can-caglar/Data-Logger-STM32/resource/HoC.png

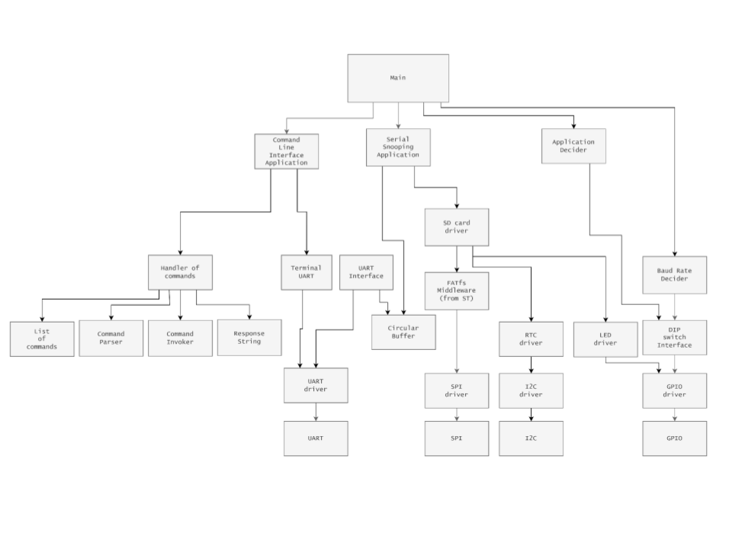
resource/HoC.png
