can-caglar/Data-Logger-STM32/resource/prototype.png

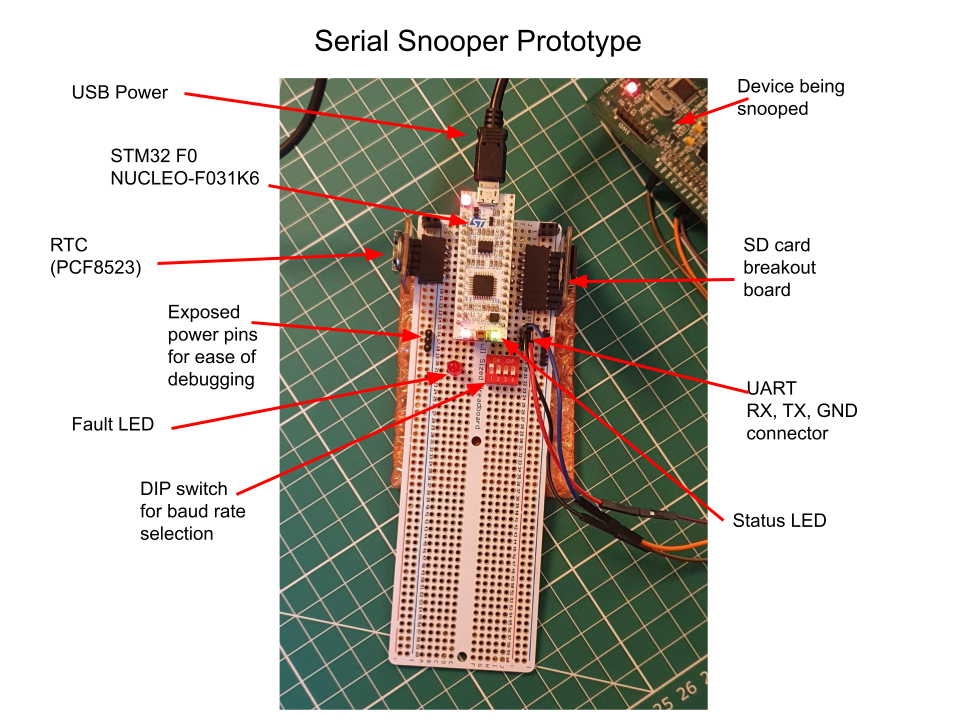
resource/prototype.png
