can-caglar/Data-Logger-STM32/src/serial_snooper/SerialSnooper.h

#ifndef SERIAL_SNOOPER_H
#define SERIAL_SNOOPER_H

#include <stdint.h>

#ifndef bool
#define bool uint8_t
#define true 1
#define false 0
#endif

enum
{
    SS_ERR_NONE,
    SS_ERR_FAULT,
};

#define MAX_TASKS 5

// Fw declare DataContext
typedef struct DataContext DataContext;

// Scheduler task function pointer
typedef void (*FnTask)(void);

void SerialSnooper_Init(void);
void SerialSnooper_Run(void);

int SerialSnooper_AddTask(FnTask func, 
    uint32_t period, bool periodic, bool enabled);

#endif
