can-caglar/Data-Logger-STM32/src/RTC/MyTimeString.c

#include "MyTimeString.h"
#include "MyRTC.h"
#include <stdio.h>
#include <string.h>

static const char* strLookup(uint8_t num);

static char ret[23];

#define LOOKUP_AMOUNT 100

static const char* const numToStrLookup[LOOKUP_AMOUNT] =
{
    "00", "01", "02", "03", "04",
    "05", "06", "07", "08", "09",
    "10", "11", "12", "13", "14",
    "15", "16", "17", "18", "19",
    "20", "21", "22", "23", "24",
    "25", "26", "27", "28", "29",
    "30", "31", "32", "33", "34",
    "35", "36", "37", "38", "39",
    "40", "41", "42", "43", "44",
    "45", "46", "47", "48", "49",
    "50", "51", "52", "53", "54",
    "55", "56", "57", "58", "59",
    "60", "61", "62", "63", "64",
    "65", "66", "67", "68", "69",
    "70", "71", "72", "73", "74",
    "75", "76", "77", "78", "79",
    "80", "81", "82", "83", "84",
    "85", "86", "87", "88", "89",
    "90", "91", "92", "93", "94",
    "95", "96", "97", "98", "99",
};

static uint32_t secondsSinceEpoch(const MyTime* time);

int MyTimeString_Init(void)
{
    MyRTC_Init();
    return 0;
}

const char* MyTimeString_GetFileName(void)
{
    // max 8 characters (+ .txt)
    // Unix timestamp, should be good for many decades
    // as of 2022
    MyTime time = MyRTC_ReadTime();
    uint32_t unixTs = secondsSinceEpoch(&time);
    sprintf(ret, "%X.txt", unixTs);
    return ret;
}

const char* MyTimeString_GetTimeStamp(void)
{
    char* strPtr = ret;
    #define maxSize 2
    char colon = ':';
    char space = ' ';
    char hyphen = '-';
    char squareOpen = '[';
    char squareClose = ']';
    MyTime time = MyRTC_ReadTime();
    // Square open
    memcpy(strPtr, &squareOpen, 1);
    strPtr += 1;
    // Year two thousand...
    const char* number = strLookup(20);    
    memcpy(strPtr, number, maxSize);
    strPtr += 2;
    // Year
    number = strLookup(time.year);
    memcpy(strPtr, number, maxSize);
    strPtr += 2;
    // Hyphen
    memcpy(strPtr, &hyphen, 1);
    strPtr += 1;
    // Month
    number = strLookup(time.month);
    memcpy(strPtr, number, maxSize);
    strPtr += 2;
    // Hyphen
    memcpy(strPtr, &hyphen, 1);
    strPtr += 1;
    // Day
    number = strLookup(time.day);
    memcpy(strPtr, number, maxSize);
    strPtr += 2;
    // Space
    memcpy(strPtr, &space, 1);
    strPtr += 1;
    // Hour
    number = strLookup(time.hour);
    memcpy(strPtr, number, maxSize);
    strPtr += 2;  
    // Colon
    memcpy(strPtr, &colon, 1);
    strPtr += 1;
    // Minute
    number = strLookup(time.minute);
    memcpy(strPtr, number, maxSize);
    strPtr += 2;  
    // Colon
    memcpy(strPtr, &colon, 1);
    strPtr += 1;
    // Second
    number = strLookup(time.second);
    memcpy(strPtr, number, maxSize);
    strPtr += 2;
    // Square close
    memcpy(strPtr, &squareClose, 1);
    strPtr += 1;
    // Space
    memcpy(strPtr, &space, 1);
    strPtr += 1;
    // Null
    *strPtr = '\0';

    return ret;
}

// Helper functions
static uint32_t secondsSinceEpoch(const MyTime* time)
{
    // Seconds passed since 1st January 1970
    uint32_t timeEpoch = 0;
    
    // year
    for (uint32_t i = 1970; i < (2000 + time->year); i++)
    {
        uint32_t days = 365;
        if ((i & 3) == 0)   // modulus 4
        {
            days = 366;
        }
        timeEpoch += (days * 86400);
    }
    // month
    for (uint32_t i = 1; i < time->month; i++)
    {
        uint32_t days = 31;
        if (i == 2)
        {
            if ((time->year & 3) == 0)
            {
                days = 29;
            }
            else
            {
                days = 28;
            }
        }
        if ((i == 4) || (i == 6) || (i == 9) || (i == 11))
        {
            days = 30;
        }
        timeEpoch += (days * 86400);
    }
    // day
    timeEpoch += (time->day - 1) * 86400;

    // hour
    timeEpoch += (time->hour * 3600);

    // minute
    timeEpoch += (time->minute * 60);

    // second
    timeEpoch += time->second;

    return timeEpoch;
}

const char* strLookup(uint8_t num)
{
    const char* ret = numToStrLookup[0];
    if (num < LOOKUP_AMOUNT)
    {
        ret = numToStrLookup[num];
    }
    return ret;
}
