can-caglar/Data-Logger-STM32/src/cli/MyProcessor.c

#include "MyProcessor.h"
#include <string.h>
#include <stdio.h>

#include "MySD.h"
#include "LED.h"
#include "MyCircularBuffer.h"
#include "MyTimeString.h"
#include "BaudDecider.h"
#include "MyRTC.h"

// preprocessor
#define MAX_RESPONSE_LEN 26
#define HELP_STR    "Usage:"

// typedefs
typedef void(*CommandPtr)(void);

// Static globals
static char cmdResponse[MAX_RESPONSE_LEN];  // this is the response from the module
// Below variables for handling incoming string
// TODO This way of string handling is messy and needs to be refactored!
static char scratchpad[MAX_RESPONSE_LEN]; // Used for string manipulation
static char scratchpad2[MAX_RESPONSE_LEN];
static char* commandPhrase;

#define MISSING_PARAM_STR   "Missing parameter!"
#define INVALID_PARAM_STR   "Invalid parameter!"

// Forward declarations

// Command handlers
static void cmdHelp(void);
static void cmdSeeAll(void);
static void cmdGetTime(void);
static void cmdSetTime(void);
static void cmdGetBR(void);

// Helper functions
int findCommand(char* cmdStr);
void updateResponse(char* newResponse);
void buildHelpString(int cmdIndex);

// Command count
typedef enum
{
    CMD_HELP,
    CMD_SEE_ALL,
    CMD_GETTIME,
    CMD_SETTIME,
    CMD_GETBR,
    CMD_COUNT   // must be last
} AllCommands_e;

//
// The command table
//
typedef struct Commands
{
    const char str[MAX_COMMAND_LEN];
    const CommandPtr fn;
    const char help[MAX_HELP_LEN];
} Commands;

const Commands commands[CMD_COUNT] =
{
    [CMD_HELP]          = {"help", cmdHelp, "<command>"},
    [CMD_SEE_ALL]       = {"seeAll", cmdSeeAll, ""},
    [CMD_GETTIME]       = {"getTime", cmdGetTime, ""},
    [CMD_SETTIME]       = {"setTime", cmdSetTime, "<yymmddhhmmss>"},
    [CMD_GETBR]         = {"getBR", cmdGetBR, ""},
};

//
void MyProcessor_HandleCommandWithString(char* str)
{
    size_t inputStrLen = strlen(str);
    if (inputStrLen >= MAX_INPUT_LEN)
    {
        updateResponse("Input too long!");
        return;
    }
    
    if (inputStrLen != 0)   
    {
        // we received a potential command...

        // break it down
        memset(scratchpad, 0, MAX_RESPONSE_LEN);
        memset(scratchpad2, 0, MAX_RESPONSE_LEN);
        strcpy(scratchpad, str);
        strcpy(scratchpad2, str);
        char* token = strtok(scratchpad, " ");
        commandPhrase = scratchpad2;
        commandPhrase += strlen(scratchpad) + 1;
        
        // look for it...
        int cmdIndex = findCommand(token);
        if (cmdIndex != -1)
        {
            // invoke it...
            commands[cmdIndex].fn();
        }
        else
        {
            sprintf(cmdResponse, "Command doesn't exist: %s", token);
        }
    }
    else
    {
        updateResponse("Received no commands.");
    }
}

const char* MyProcessor_GetResponseMessage(void)
{
    return cmdResponse;
}

/************** The commands ***************/

static void cmdHelp(void)
{
    char* token = strtok(NULL, " ");
    if (token != NULL)
    {
        // help for some command
        int cmdIndex = findCommand(token);
        if (cmdIndex != -1)
        {
            // build help string
            buildHelpString(cmdIndex);
        }
        else
        {
            // command not found
            sprintf(cmdResponse, "No such command exists: %s", token);
        }
    }
    else
    {
        // help for the "help" command
        buildHelpString(CMD_HELP);
    }
}

static void cmdSeeAll(void)
{
    scratchpad[0] = 0;
    for (int i = 0; i < CMD_COUNT; i++)
    {
        strcat(scratchpad, commands[i].str);
        if (i < CMD_COUNT - 1)
        {
            strcat(scratchpad, " ");
        }
    }
    updateResponse(scratchpad);
}

static void cmdGetTime(void)
{
    MyTimeString_Init();
    strcpy(cmdResponse, MyTimeString_GetTimeStamp());
}

static void cmdSetTime(void)
{
    const char* token = strtok(NULL, " ");
    const char* timeToSet = token;
    if (timeToSet != NULL)
    {
        if (strlen(timeToSet) != 12)
        {
            updateResponse(INVALID_PARAM_STR);
            return;
        }
        char timeValues[12][3] = { 0 };
        for (int i = 0; i < 12; i++)
        {
            for (int j = 0; j < 2; j++)
            {
                timeValues[i][j] = *timeToSet;
                timeToSet++;
            }
        }
        MyRTC_Init();
        MyTime newTime = { 0 };
        newTime.year = atoi(timeValues[0]);
        newTime.month = atoi(timeValues[1]);
        newTime.day = atoi(timeValues[2]);
        newTime.hour = atoi(timeValues[3]);
        newTime.minute = atoi(timeValues[4]);
        newTime.second = atoi(timeValues[5]);

        if (MyRTC_WriteTime(&newTime) == 0)
        {
            updateResponse("Time has been set.");
        }
        else
        {
            updateResponse("Time not set. RTC error.");
        }
    }
    else
    {
        updateResponse("Missing parameter!");
    }
}

static void cmdGetBR(void)
{
    BaudDecider_Init();
    uint32_t br = BaudDecider_GetBR();
    sprintf(cmdResponse, "Baud Conf: %u", br);
}

/********************* helper functions **************/

int findCommand(char* cmdStr)
{
    for (unsigned int i = 0; i < CMD_COUNT; i++)
    {
        if (strcmp(commands[i].str, cmdStr) == 0)
        {
            return i;
        }
    }
    return -1;
}

void updateResponse(char* newResponse)
{
    // TODO, limit response if it's too long
    strcpy(cmdResponse, newResponse);
}

void buildHelpString(int cmdIndex)
{
    char separator = ' ';
    if (strcmp(commands[cmdIndex].help, "") == 0)
    {
        separator = '\0';
    }
    sprintf(cmdResponse, "%s %s%c%s", 
        HELP_STR,
        commands[cmdIndex].str, 
        separator,
        commands[cmdIndex].help);
}
