can-caglar/Data-Logger-STM32/src/MyApp.c

#include "MyApp.h"
#include "MyCLI.h"
#include "Loop.h"
#include "AppDecider.h"
#include "MyScheduler.h"
#include "SystemOperations.h"
#include "main.h"

// Ceedling has its own main function
#ifndef TEST
#define runApp main
#endif

/*
int main(void)
*/
int runApp(void)
{
    int app = initialise();
    runInfiniteLoop(&app);
}

int initialise(void)
{
    int app;
    CubeMX_SystemInit(CMX_FATFS);   // needs a 1s delay
    AppDecider_Init();
    
    if (AppDecider_Decide() == APP_CLI)
    {
        // The CLI application
        MyCLI_Init();
        app = APP_CLI;
    }
    else
    {
        // The Serial Snooping application
        // CubeMX_SystemInit(CMX_UART);
        MyScheduler_Init();
        SystemOperations_Init();
        MyScheduler_AddTask(SystemOperations_OpenLogFile,
            0, true, true);
        MyScheduler_AddTask(SystemOperations_WriteSD, 
            0, true, true);
        MyScheduler_AddTask(SystemOperations_FlushSD,
            FLUSH_TIME_MS, true, true);
        MyScheduler_AddTask(SystemOperations_ConfigureUart,
            0, true, true);
        app = APP_SNOOPING;
    }
    return app;
}

void runInfiniteLoop(const int* const app)
{
    if (*app == APP_CLI)
    {
        LOOP
        {
            MyCLI_Run();
        }
    }
    else
    {
        LOOP
        {
            MyScheduler_Run();
        }
    }
}
