can-caglar/Data-Logger-STM32/src/serial_snooper/DataHolder.h

#ifndef DATA_HOLDER_H
#define DATA_HOLDER_H

#include <stdint.h>

// Encapsulates the system information
// that is needed for the serial snooper.

uint8_t DH_IsThereNewData(void);
uint8_t DH_GetLatestData(void);
const char* DH_GetFileName(void);
const char* DH_GetTimestampString(void);
uint32_t DH_GetOpenedFileSize(void);

#endif
