can-caglar/Data-Logger-STM32/src/dip_switch/AppDecider.h

#ifndef APP_DECIDER_H_INCLUDED
#define APP_DECIDER_H_INCLUDED

typedef enum Applications
{
    APP_CLI,
    APP_SNOOPING
} Applications;

void AppDecider_Init(void);
Applications AppDecider_Decide(void);

#endif
