can-caglar/Data-Logger-STM32/src/common/MyCommon.c

#include "MyCommon.h"

const GPIO_Pin_Mask_t pin0_mask = (0x1UL << 0);
const GPIO_Pin_Mask_t pin1_mask = (0x1UL << 1);
const GPIO_Pin_Mask_t pin2_mask = (0x1UL << 2);
const GPIO_Pin_Mask_t pin3_mask = (0x1UL << 3);
const GPIO_Pin_Mask_t pin4_mask = (0x1UL << 4);
const GPIO_Pin_Mask_t pin5_mask = (0x1UL << 5);
const GPIO_Pin_Mask_t pin6_mask = (0x1UL << 6);
const GPIO_Pin_Mask_t pin7_mask = (0x1UL << 7);
const GPIO_Pin_Mask_t pin8_mask = (0x1UL << 8);
const GPIO_Pin_Mask_t pin9_mask = (0x1UL << 9);
const GPIO_Pin_Mask_t pin10_mask = (0x1UL << 10);
const GPIO_Pin_Mask_t pin11_mask = (0x1UL << 11);
const GPIO_Pin_Mask_t pin12_mask = (0x1UL << 12);
const GPIO_Pin_Mask_t pin13_mask = (0x1UL << 13);
const GPIO_Pin_Mask_t pin14_mask = (0x1UL << 14);
const GPIO_Pin_Mask_t pin15_mask = (0x1UL << 15);
const GPIO_Pin_Mask_t pins_all_mask = (0xFFFFUL);
