can-caglar/Data-Logger-STM32/test/fakes/fakefilesystem.c

#include "fakefilesystem.h"
#include <string.h>
#include <stdint.h>
#include <stdio.h>

typedef uint8_t bool;
#ifndef true
#define true 1
#endif
#ifndef false
#define false 0
#endif

typedef struct File_t
{
    char name[FFS_MAX_FILENAME];
    char data[FFS_MAX_FILESIZE];
    int fileSize;
    int filePointer;
} File_t;

struct
{
    File_t files[FFS_MAX_FILES];
} internalState;

/* Private functions */

File_t* findFile(const char* fileName);
File_t* findEmptyFileSlot(void);

/* Public function definitions */

void fakefilesystem_reset(void)
{
    memset(&internalState, 0, sizeof(internalState));
}

int fakefilesystem_fileExists(const char* fileName)
{
    return findFile(fileName) != NULL;
}

int fakefilesystem_fileSize(const char* name)
{
    int size = 0;
    File_t* file = findFile(name);
    if (file)
    {
        size = file->fileSize;
    }
    return size;
}

void fakefilesystem_createFile(const char* fileName)
{
    File_t* file = findFile(fileName);
    if (file == NULL)
    {
        file = findEmptyFileSlot();
        if (file)
        {
            strncpy(file->name, fileName, FFS_MAX_FILENAME);
        }
    }
}

void fakefilesystem_deleteFile(const char* fileName)
{
    File_t* file = findFile(fileName);
    if (file != NULL)
    {
        memset(file, 0, sizeof(*file));
    }
}

// Reads from where the file pointer is.
// Use fakefilesystem_seek to modify it.
const char* fakefilesystem_readfile(const char* fileName)
{
    File_t* file = findFile(fileName);
    if (file)
    {
        return file->data + file->filePointer;
    }
    return "";
}

void fakefilesystem_writeFile(const char* fileName, const char* data)
{
    File_t* file = findFile(fileName);
    if (file != NULL)
    {
        char* writeIndex = file->data + file->filePointer;
        strcpy(writeIndex, data);
        file->filePointer += strlen(data);
        file->fileSize = strlen(file->data);
    }
}

void fakefilesystem_seek(const char* fileName, int pos)
{
    File_t* file = findFile(fileName);
    if (file != NULL)
    {
        if (pos == FFS_BEGIN)
        {
            file->filePointer = 0;
        }
        else if (pos <= FFS_END)
        {
            file->filePointer = file->fileSize;
        }
        else
        {
            if (pos > file->fileSize)
            {
                pos = file->fileSize;
            }
            file->filePointer = pos;
        }
    }
}

/* Private function definitions */

File_t* findFile(const char* fileName)
{
    File_t* file = NULL;
    for (int i = 0; i < FFS_MAX_FILES; i++)
    {
        if (strcmp(fileName, internalState.files[i].name) == 0)
        {
            file = &internalState.files[i];
            break;
        }
    }
    return file;
}

File_t* findEmptyFileSlot(void)
{
    File_t* file = NULL;
    int i;
    for (i = 0; i < FFS_MAX_FILES; i++)
    {
        if (strcmp(internalState.files[i].name, "") == 0)
        {
            file = &internalState.files[i];
            break;
        }
    }
    return file;
}

void fakefilesystem_dump(void)
{
    printf("Printing file system contents...\n");
    for (size_t i = 0; i < FFS_MAX_FILES; i++)
    {
        if (strcmp(internalState.files[i].name, "") != 0)
        {
            File_t* thisFile = &internalState.files[i];
            printf("Filename: \"%s\"\n", thisFile->name);
            printf("Contents: ");
            int count = printf("%.20s", thisFile->data);
            if (count == 20)
            {
                printf("{truncated}");
            }
            printf("\n");
            printf("Size: %u\n", thisFile->fileSize);
            printf("File Ptr: %u\n", thisFile->filePointer); 
            printf("--------------\n");
        }
    }
    printf("Finished printing\n");
}
