can-caglar/Data-Logger-STM32/test/test_Application.c

#include "unity.h"
#include "MyApp.h"
#include "mock_MyCLI.h"
#include "mock_AppDecider.h"
#include "mock_SerialSnooper.h"
#include "mock_main.h"
#include "Loop.h"

void test_App_CLI(void)
{
    LOOP_COUNT(3);  // expecting 3 times round the loop

    CubeMX_SystemInit_Expect(CMX_FATFS);
    AppDecider_Init_Expect();
    AppDecider_Decide_ExpectAndReturn(APP_CLI);

    MyCLI_Init_Expect();
    // expecting 3 calls
    MyCLI_Run_Expect();
    MyCLI_Run_Expect();
    MyCLI_Run_Expect();

    runApp();
}

void test_App_SnoopingSuccess(void)
{
    LOOP_COUNT(3);  // expecting 3 times round the loop

    CubeMX_SystemInit_Expect(CMX_FATFS);
    AppDecider_Init_Expect();
    AppDecider_Decide_ExpectAndReturn(APP_SNOOPING);

    SerialSnooper_Init_ExpectAndReturn(SS_SUCCESS);
    // expecting 3 calls
    SerialSnooper_Run_Expect();
    SerialSnooper_Run_Expect();
    SerialSnooper_Run_Expect();

    runApp();
}

void test_App_SnoopingFailInit(void)
{
    LOOP_COUNT(3);  // expecting 3 times round the loop

    CubeMX_SystemInit_Expect(CMX_FATFS);
    AppDecider_Init_Expect();
    AppDecider_Decide_ExpectAndReturn(APP_SNOOPING);

    SerialSnooper_Init_ExpectAndReturn(SS_FAIL);
    
    // expecting 0 calls to SerialSnooper_Run

    runApp();
}
